tl5915/Trimix-Analyser/include/qr_code_bitmap.h

#pragma once
#include <pgmspace.h>

const unsigned char qrCodeBitmap[] PROGMEM = {
	0xff, 0xff, 0x80, 0xc7, 0xc3, 0x9f, 0xff, 0xf0, 0xff, 0xff, 0x80, 0xc7, 0xc3, 0x9f, 0xff, 0xf0, 
	0xff, 0xff, 0x9f, 0xbc, 0x81, 0x1f, 0xff, 0xf0, 0xe0, 0x03, 0x9f, 0x38, 0x00, 0x1c, 0x00, 0x70, 
	0xe0, 0x03, 0x9f, 0x38, 0x00, 0x1c, 0x00, 0x70, 0xe7, 0xf3, 0x9c, 0x38, 0x33, 0x9c, 0xfe, 0x70, 
	0xe7, 0xf3, 0x9c, 0x38, 0x33, 0x9c, 0xfe, 0x70, 0xe7, 0xf3, 0x9f, 0xe6, 0x3f, 0x9c, 0xfe, 0x70, 
	0xe7, 0xf3, 0x9f, 0xc6, 0x3f, 0x9c, 0xfe, 0x70, 0xe7, 0xf3, 0x9f, 0xc7, 0x7f, 0x9c, 0xfe, 0x70, 
	0xe7, 0xf3, 0x80, 0xc7, 0xc0, 0x1c, 0xfe, 0x70, 0xe7, 0xf3, 0x80, 0xc7, 0xc0, 0x1c, 0xfe, 0x70, 
	0xe0, 0x03, 0x80, 0x01, 0xf0, 0x1c, 0x00, 0x70, 0xe0, 0x03, 0x80, 0x01, 0xf0, 0x1c, 0x00, 0x70, 
	0xff, 0xff, 0x98, 0xc7, 0x71, 0x9f, 0xff, 0xf0, 0xff, 0xff, 0x9c, 0xc6, 0x33, 0x9f, 0xff, 0xf0, 
	0xff, 0xff, 0x9c, 0xc6, 0x73, 0x9f, 0xff, 0xf0, 0x00, 0x00, 0x1f, 0xc1, 0xc3, 0x80, 0x00, 0x00, 
	0x00, 0x00, 0x1f, 0xc1, 0xc3, 0x80, 0x00, 0x00, 0xc0, 0x03, 0x9f, 0x06, 0x7f, 0xfc, 0x3f, 0xc0, 
	0xc0, 0x03, 0x9f, 0x06, 0x3f, 0xfc, 0x3f, 0xc0, 0xc0, 0x23, 0xff, 0x86, 0x3f, 0xf8, 0x3f, 0xc0, 
	0xc0, 0x3c, 0x63, 0xc6, 0x3f, 0xe0, 0xff, 0xc0, 0xe0, 0x3e, 0x63, 0xc6, 0x3f, 0xe0, 0xff, 0xc0, 
	0xfe, 0x03, 0xe3, 0x00, 0x0e, 0x1f, 0x39, 0xf0, 0xfe, 0x03, 0xe3, 0x00, 0x0c, 0x1f, 0x39, 0xf0, 
	0x3e, 0x0e, 0x43, 0xc6, 0x3f, 0x89, 0xf8, 0x70, 0x3e, 0x0c, 0x00, 0xc6, 0x3f, 0x80, 0xf8, 0x30, 
	0x3f, 0x0e, 0x00, 0xe6, 0x7f, 0x80, 0xf8, 0x30, 0x07, 0xf3, 0x9c, 0x39, 0xf3, 0xfc, 0x00, 0x30, 
	0x07, 0xf3, 0x9c, 0x39, 0xf3, 0xfc, 0x00, 0x70, 0xc7, 0xfe, 0x7f, 0xe7, 0xfe, 0x00, 0x01, 0xc0, 
	0xc7, 0xfc, 0x7f, 0xc7, 0xfc, 0x00, 0x01, 0xc0, 0xc7, 0xfe, 0xff, 0xc7, 0xfc, 0x02, 0x11, 0xc0, 
	0xc0, 0x03, 0xe3, 0xc1, 0xfc, 0x63, 0x39, 0xf0, 0xc0, 0x03, 0xe7, 0xc1, 0xfe, 0x63, 0x39, 0xf0, 
	0xc6, 0x00, 0x7f, 0xc7, 0xf3, 0x80, 0xe6, 0x70, 0xc6, 0x00, 0x7f, 0xc7, 0xf3, 0x80, 0xc6, 0x30, 
	0xc0, 0x0f, 0xf7, 0x87, 0x73, 0xff, 0xc6, 0x20, 0xc0, 0x0f, 0xe3, 0x06, 0x33, 0xff, 0xc6, 0x00, 
	0xc0, 0x0f, 0xe7, 0x06, 0x33, 0xff, 0xc6, 0x00, 0x00, 0x00, 0x1f, 0x00, 0x0f, 0x80, 0xc6, 0x00, 
	0x00, 0x00, 0x1f, 0x00, 0x0f, 0x80, 0xe6, 0x00, 0xff, 0xff, 0x80, 0x07, 0xf3, 0x9c, 0xf8, 0x30, 
	0xff, 0xff, 0x80, 0x07, 0xf3, 0x9c, 0xf8, 0x30, 0xff, 0xff, 0x80, 0x1f, 0xf3, 0x98, 0xf8, 0x30, 
	0xe0, 0x03, 0x80, 0x38, 0x33, 0x80, 0xc0, 0x00, 0xe0, 0x03, 0x80, 0x38, 0x33, 0x80, 0xe0, 0x00, 
	0xe7, 0xf3, 0x83, 0x38, 0x0f, 0xff, 0xfe, 0x30, 0xe7, 0xf3, 0x83, 0x38, 0x0f, 0xff, 0xfe, 0x30, 
	0xe7, 0xf3, 0x83, 0xef, 0x84, 0x3f, 0xbf, 0xf0, 0xe7, 0xf3, 0x83, 0xc7, 0xc0, 0x1f, 0x39, 0xf0, 
	0xe7, 0xf3, 0x83, 0xc7, 0xc0, 0x1f, 0x39, 0xf0, 0xe7, 0xf3, 0x83, 0xc1, 0xf0, 0x60, 0x06, 0x70, 
	0xe7, 0xf3, 0x83, 0xc1, 0xf0, 0x60, 0x06, 0x30, 0xe0, 0x03, 0x83, 0xc7, 0xcf, 0x9f, 0xc0, 0x30, 
	0xe0, 0x03, 0x83, 0xc7, 0xcf, 0x9f, 0xc0, 0x30, 0xff, 0xff, 0x87, 0xef, 0xcf, 0x9f, 0xf0, 0x30, 
	0xff, 0xff, 0x9f, 0x3f, 0xcf, 0x9c, 0x38, 0x30, 0xff, 0xff, 0x9f, 0x3f, 0xcf, 0x9c, 0x38, 0x30
};
